pierre-muth/NeonPixel/kicad/neonpixelmatrix/NPM_PCB.PNG

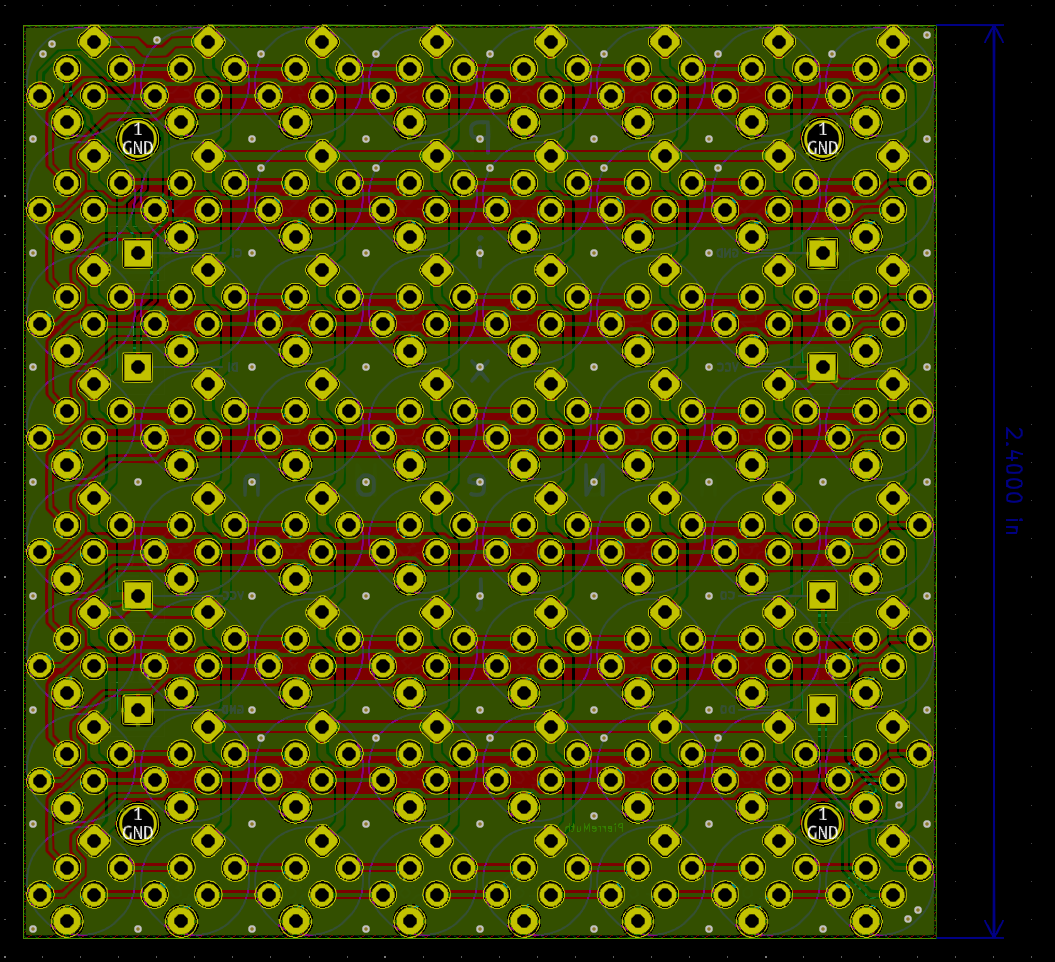
kicad/neonpixelmatrix/NPM_PCB.PNG
