pierre-muth/NeonPixel/plateformIO/NeonPixelTest01/include/Muth01_4.h

const uint8_t Muth014pt7bBitmaps[] PROGMEM = {
  0xFF, 0xF3, 0xFC, 0x63, 0x18, 0xC6, 0x31, 0x8C, 0x7E, 0x57, 0xD5, 0xF5,
  0x00, 0xFC, 0x63, 0x18, 0xC6, 0x31, 0x8C, 0x7E, 0xFC, 0x63, 0x18, 0xC6,
  0x31, 0x8C, 0x7E, 0x7B, 0x2C, 0x18, 0xCF, 0x2C, 0x9D, 0xFC, 0x63, 0x18,
  0xC6, 0x31, 0x8C, 0x7E, 0x7B, 0x6D, 0xB3, 0xCD, 0xB6, 0xDE, 0x25, 0x5D,
  0x52, 0x00, 0xFC, 0x63, 0x18, 0xC6, 0x31, 0x8C, 0x7E, 0xF6, 0xE0, 0xF0,
  0x11, 0x22, 0x44, 0x88, 0x7B, 0x3C, 0xF3, 0xCF, 0x3C, 0xDE, 0x7D, 0xB6,
  0xDB, 0x7A, 0x30, 0xC3, 0x39, 0x8C, 0x3F, 0x7B, 0x30, 0xCE, 0x0C, 0x3C,
  0xDE, 0x18, 0x65, 0x96, 0x9B, 0xF1, 0x86, 0xFB, 0x0C, 0x3E, 0x0C, 0x30,
  0xFE, 0x39, 0x8C, 0x3E, 0xCF, 0x3C, 0xDE, 0xFC, 0x31, 0x86, 0x30, 0xC3,
  0x0C, 0x7B, 0x3C, 0xDE, 0xCF, 0x3C, 0xDE, 0x7B, 0x3C, 0xF3, 0x7C, 0x31,
  0x9C, 0xF0, 0xF0, 0xFC, 0x63, 0x18, 0xC6, 0x31, 0x8C, 0x7E, 0xFC, 0x63,
  0x18, 0xC6, 0x31, 0x8C, 0x7E, 0xFC, 0x63, 0x18, 0xC6, 0x31, 0x8C, 0x7E,
  0xFC, 0x63, 0x18, 0xC6, 0x31, 0x8C, 0x7E, 0x7B, 0x30, 0xC6, 0x30, 0x80,
  0x0C, 0xFC, 0x63, 0x18, 0xC6, 0x31, 0x8C, 0x7E, 0x30, 0xC5, 0x96, 0x5B,
  0xF8, 0xE3, 0xFB, 0x3C, 0xFE, 0xCF, 0x3C, 0xFE, 0x7E, 0x71, 0x8C, 0x63,
  0x2E, 0xFB, 0x3C, 0xF3, 0xCF, 0x3C, 0xFE, 0xFE, 0x31, 0xEC, 0x63, 0x1F,
  0xFE, 0x31, 0xEC, 0x63, 0x18, 0x7F, 0x1C, 0x30, 0xDF, 0x3C, 0xDD, 0xCF,
  0x3C, 0xFF, 0xCF, 0x3C, 0xF3, 0xFF, 0xFF, 0x18, 0xC6, 0x31, 0x8E, 0x6E,
  0xC7, 0x2D, 0x3C, 0xDB, 0x6C, 0xF3, 0xC3, 0x0C, 0x30, 0xC3, 0x0C, 0x3F,
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
  {   192,   5,   8,   7,    0,   -7 },   // 0x46 'F'
  {   197,   6,   8,   7,    0,   -7 },   // 0x47 'G'
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

const GFXfont Muth014pt7b PROGMEM = {
  (uint8_t  *)Muth014pt7bBitmaps,
  (GFXglyph *)Muth014pt7bGlyphs,
  0x20, 0x7E, 9 };

// Approx. 1174 bytes
